ensonic/octacon/src/midi_io.cpp

// midi handling code

#include <debug.h>
#include <knobs.h>
#include <leds.h>
#include <midi_io.h>
#include <ui.h>

extern Debug dbg;
extern Leds leds;
extern UI ui;
extern Knobs knobs;

Adafruit_USBD_MIDI usbMidi;

//midi::MidiInterface<midi::SerialMIDI<Adafruit_USBD_MIDI>> MIDI;

static void midiControlChangeCB(uint8_t channel, uint8_t cc, uint8_t value) {
    int ix = -1;
    int v = value;
#ifdef CTRL_HIRES
    if (cc >=  CC_MSB_ValueBase && cc < CC_MSB_ValueBase + 8) {
        ix = cc - CC_MSB_ValueBase;
        v <<= 7;
    }
    if (cc >=  CC_LSB_ValueBase && cc < CC_LSB_ValueBase + 8) {
        ix = cc - CC_LSB_ValueBase;
        v += knobs.getValue(ix);
    }
else
    if (cc >=  CC_MSB_ValueBase && cc < CC_MSB_ValueBase + 8) {
        ix = cc - CC_MSB_ValueBase;
    }
#endif
    if (ix >= 0) {
        knobs.setValue(ix, v);
        ui.setValue(ix, v);
    }
}

static void midiSysExParamName(byte *data, unsigned size) {
    // param-ix, length, data
    if (size < 2) {
        dbg.printf("sysexcmd-%u too short\n", SysExCmd::ParamName);
        return;
    }
    ui.setName(data[0], (char *)(&data[2]), data[1]);
}

static void midiSysExPrettyValue(byte *data, unsigned size) {
    // param-ix, length, data
    if (size < 2) {
        dbg.printf("sysexcmd-%u too short\n", SysExCmd::PrettyValue);
        return;
    }
    ui.setPrettyValue(data[0], (char *)(&data[2]), data[1]);
}

static void midiSysExDawSync(byte *data, unsigned size) {
    // on/off
    if (size < 1) {
        dbg.printf("sysexcmd-%u too short\n", SysExCmd::DawSync);
        return;
    }
    ui.enableExtInfo(data[0]>0);
    if (!data[0]) {
        // reset addition modes when exiting daw-mode
        leds.setPattern(0);
        ui.setInfo("", 0);
    }
}

static void midiSysExLedPattern(byte *data, unsigned size) {
    // pattern
    if (size < 1) {
        dbg.printf("sysexcmd-%u too short\n", SysExCmd::LedPattern);
        return;
    }
    leds.setPattern(data[0]);
}

static void midiSysExInfo(byte *data, unsigned size) {
    // length, data
    if (size < 1) {
        dbg.printf("sysexcmd-%u too short\n", SysExCmd::Info);
        return;
    }
    ui.setInfo((char *)(&data[1]), data[0]);
}

static void midiSysExTicks(byte *data, unsigned size) {
   // param-ix, value
   if (size < 2) {
       dbg.printf("sysexcmd-%u too short\n", SysExCmd::Ticks);
       return;
   }
   ui.setTicks(data[0], data[1]);
}

static void midiSysExFlags(byte *data, unsigned size) {
   // param-ix, value
   if (size < 2) {
       dbg.printf("sysexcmd-%u too short\n", SysExCmd::Ticks);
       return;
   }
   ui.setFlags(data[0], data[1]);
}

static void midiSysExCB(byte * data, unsigned size) {
    // min size is 'F0 7D` + cmd + 'F7'
    if (size < 4) {
        dbg.println("sysex too short");
        return;
    }
    // bad sysex
    if (data[0] != 0xF0 || data[1] != 0x7D || data[size-1] != 0xF7) {
        dbg.println("bad sysex");
        return;
    }
    auto cmd = SysExCmd(data[2]);
    data=&data[3]; size -=4;
    switch(cmd) {
        case SysExCmd::ParamName:
            midiSysExParamName(data, size);
            break;
        case SysExCmd::PrettyValue:
            midiSysExPrettyValue(data, size);
            break;
        case SysExCmd::DawSync:
            midiSysExDawSync(data, size);
            break;
        case SysExCmd::LedPattern:
            midiSysExLedPattern(data, size);
            break;
        case SysExCmd::Info:
            midiSysExInfo(data, size);
            break;
        case SysExCmd::Ticks:
            midiSysExTicks(data, size);
            break;
        case SysExCmd::Flags:
            midiSysExFlags(data, size);
            break;
        default:
            dbg.println("sysex: unknown cmd");
            break;
    }
}

MidiIO::MidiIO(void) : midiTransport(usbMidi), midiInterface((MidiTransport&)midiTransport) {}

void MidiIO::init(void) {
    TinyUSBDevice.setManufacturerDescriptor("Ensonic");
    TinyUSBDevice.setProductDescriptor("Octacon");
    if (!usbMidi.begin()) {
        dbg.println("Starting usbMidi failed");
    }
    midiInterface.begin(MIDI_CHANNEL_OMNI);
    midiInterface.turnThruOff();
    midiInterface.setHandleControlChange(midiControlChangeCB);
    midiInterface.setHandleSystemExclusive(midiSysExCB);
    while( !TinyUSBDevice.mounted() ) delay(1);
}

void MidiIO::tick(void) {
    midiInterface.read();
}

void MidiIO::sendValueCC(uint8_t cc, int v) {
#ifdef CTRL_HIRES    
    midiInterface.sendControlChange(CC_MSB_ValueBase + cc, v>>7, 1);
    midiInterface.sendControlChange(CC_LSB_ValueBase + cc, v & 127, 1);
#else
    midiInterface.sendControlChange(CC_MSB_ValueBase + cc, v, 1);
#endif
}

void MidiIO::sendButtonCC(uint8_t cc, int v) {
    midiInterface.sendControlChange(CC_ButtonBase + cc, v, 1);
}
