ensonic/octacon/src/ui.cpp

// display layout code

#include <debug.h>
#include <ui.h>

extern Debug dbg;

UI::UI(U8G2 *d1, U8G2 *d2) : d1(d1), d2(d2) {}

void UI::init(void) {
    initPage(d1);
    initPage(d2);

    // TODO: make this an "about" page and also show version?
    // we could report via sysex, but also trigger by holding buttons
    // If we feel crazy, we can also embed a pong game :)
    const char *logo = "OCTACON";
    auto w = d1->getStrWidth(logo);
    auto x = 64 - w; // we print with double size

    d1->clearBuffer();
    d1->drawStrX2(x,32+8, logo);
    d1->updateDisplay(); // display refresh: 3043 µs
    if(d2) {
        d2->clearBuffer();
        d2->drawStrX2(x,32+8, logo);
        d2->updateDisplay();
    }
    delay(100);
}

void UI::begin() {
    enableExtInfo(0);
}

void UI::draw(unsigned ix) {
    if (!extInfo) {
        for (unsigned i=0; i<numParams; i++) {
            p[i].prettyvalue = String(u8x8_u16toa(p[i].value, UI_DIGITS));
        }
    }
    if (!(ix & 2)) {
        this->drawPage(d2, p[0], p[1], p[4], p[5], info1);
    } else {
        this->drawPage(d1, p[2], p[3], p[6], p[7], info2);
    }
}

void UI::setName(unsigned ix, char *str, unsigned len) {
    if (ix >= numParams) {
        dbg.printf("ix=%u > %u\n", ix, numParams);
        return;
    }
    p[ix].name = String(str, len);
    draw(ix);
}

void UI::setPrettyValue(unsigned ix, char *str, unsigned len) {
    if (ix >= numParams) {
        dbg.printf("ix=%u > %u\n", ix, numParams);
        return;
    }
    p[ix].prettyvalue = String(str, len);
    draw(ix);
}

void UI::setValue(unsigned ix, unsigned value) {
    if (ix >= numParams) {
        dbg.printf("ix=%u > %u\n", ix, numParams);
        return;
    }
    p[ix].value = value / UI_SCALE;
    draw(ix);
}

void UI::enableExtInfo(bool enable) {
    extInfo = enable;
    if (!extInfo) {
        const String ixstr[] = {"1", "2", "3", "4", "5", "6", "7", "8"};
        for (unsigned i=0; i<numParams; i++) {
            p[i].name = String("Param ") + ixstr[i];
        }
    }
    draw(0);
    draw(2);
}

void UI::setInfo(const char *str, unsigned len) {
    int li = sizeof(info1) - 1;
    for (unsigned i=0; i < sizeof(info1); i++) {
        info1[i]='\0';
        info2[i]='\0';
    }

    // copy string into both display parts
    int sp = 0, dp = 0;
    while(true) {
        if (sp == len || dp == li) {
            break;
        }
        info1[dp]=str[sp];
        if (d1->getStrWidth(info1)>=128) {
            break;
        }
        dp++; sp++;
    }
    if (sp < len) {
        dp = 0;
        while(true) {
            if (sp == len || dp == li) {
                break;
            }
            info2[dp]=str[sp];
            if (d1->getStrWidth(info2)>=128) {
                break;
            }
            dp++; sp++;
        }
    }
    draw(0);
    draw(2);
}

void UI::setTicks(unsigned ix, unsigned ticks) {
    if (ix >= numParams) {
        dbg.printf("ix=%u > %u\n", ix, numParams);
        return;
    }
    p[ix].ticks = ticks;
    draw(ix);
}

void UI::setFlags(unsigned ix, unsigned flags) {
    if (ix >= numParams) {
        dbg.printf("ix=%u > %u\n", ix, numParams);
        return;
    }
    p[ix].flags = flags;
    draw(ix);
}

// private impl

void UI::initPage(U8G2 *d) {
    if (!d) return;

    d->begin();
    // less flicker: 9.5 Timing & Driving Scheme Setting Command Table 
    d->sendF("ca", 0xd5, 0xF0); 
    d->setContrast(200);  //  Brightness setting from 0 to 255
    d->setFont(
    // 6 pixel
    // u8g2_font_spleen5x8_mf // same width as: u8g2_font_helvR08_tf
    // 7 pixel
    u8g2_font_NokiaSmallPlain_tf
    // 8 pixel
    // u8g2_font_helvR08_tf // not monospaced, can fit more text
    // u8g2_font_spleen6x12_mf // m=monospaced,f= full charset
    );
    d->setFontMode(1); // make transparent (no bg)
}

void UI::drawPage(U8G2 *d, UIParam &p0, UIParam &p1, UIParam &p2, UIParam &p3, char *str) {
    if (!d) return;

    d->clearBuffer();
    drawColumn(d, 0, p0, p2);
    drawColumn(d, 65, p1, p3);
    d->setClipWindow(0, 32-4, 127, 32+4);
    d->drawStr(0, 32+3, str);
    d->updateDisplay(); // display refresh: 3059 µs
    // TODO: if we update from the callback, we maybe send a bit mask for which value changed
    // https://github.com/olikraus/u8g2/wiki/u8g2reference#updatedisplayarea
    //unsigned ts0 = micros();
    //d->updateDisplayArea(0,0,8,4); // display refresh: 827 µs
    //ts0=micros()-ts0;
    //dbg.printf("refresh: %u µs\n", ts0);
}

void UI::drawColumn(U8G2 *d, unsigned x, UIParam &p0, UIParam &p1) {
    drawParam(d, x, 0, 24, p0);
    drawParam(d, x, 49, 46, p1);
}

void UI::drawParam(U8G2 *d, unsigned x, unsigned by, unsigned ly, UIParam &p) {
    unsigned w = 64-2;
    d->setDrawColor(1);
    d->setMaxClipWindow();
    // value box
    d->drawFrame(x, by, 63, 14);
    d->drawBox(x, by + 1, p.value/2, 13);
    // param name
    d->setClipWindow(x, ly - 10, x + w, ly+1);
    d->drawStr(x, ly, p.name.c_str());  // 24 = 16 + 7 + 1
    // pretty name
    d->setDrawColor(2);
    d->setClipWindow(x + 1, by + 2, x + (w - 1), by + 13);
    d->drawStr(x + 2, by + 10, p.prettyvalue.c_str());
    // tick marks
    d->setMaxClipWindow();
    if (p.ticks > 0) {
        float s = 63.5 / (float)p.ticks;
        if (s > 1.0) {
            for (unsigned t = 1; t < p.ticks; t ++) {
                unsigned xp =  x + (int)(t * s);
                d->drawPixel(xp, by + 12);
                d->drawPixel(xp, by + 13);
            }
        }
    }
    // draw automation hint
    if (p.flags & 0x01) {
        d->setDrawColor(0);
        d->drawTriangle(x + 58, by, x + 63, by, x + 63, by + 5);
        d->setDrawColor(1);
        d->drawLine(x + 57, by, x + 63, by + 6);
    }
}
